jeffmhopkins/esp32-s3-touch-amoled-1.8-case/reference/waveshare-dimensions.webp

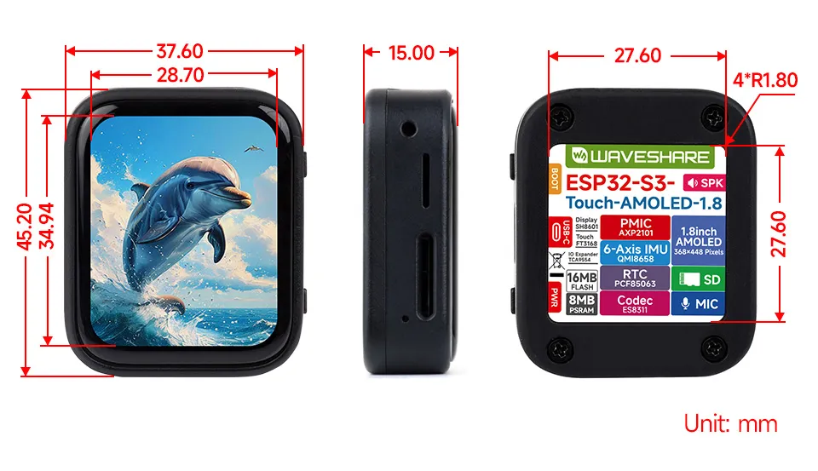
reference/waveshare-dimensions.webp
