jeffmhopkins/esp32-s3-touch-amoled-1.8-case/renders/photoreal/screens/screen_landscape.png

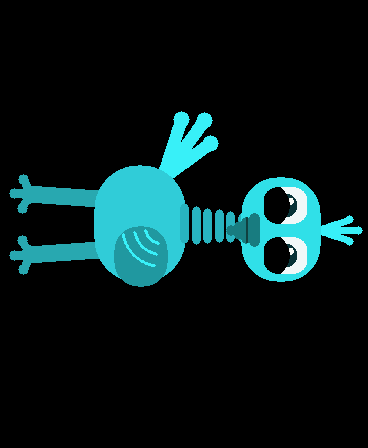
renders/photoreal/screens/screen_landscape.png
