jeffmhopkins/esp32-s3-touch-amoled-1.8-case/renders/src/fig_stand_joint.scad

// Where the head sits in the box: a side wall cut through a lock screw, drawn
// square to the head (the whole stand tilted back level).
include <../../amoled18_back_plate.scad>
use <annot.scad>
show_part = false;
$fn = 64; $k = 0.22;
lx = lock_xs[len(lock_xs) - 1];   // cut through this lock screw
v = "right"; x = lx + 2.6; t = 0.45;
m_inv = [[sc, 0, ss, -ss * stand_zh], [0, 1, 0, 0], [-ss, 0, sc, -sc * stand_zh], [0, 0, 0, 1]];
module slice() intersection() { children(); translate([lx - 0.2, 15, -6]) cube([0.4, 10, 13]); }
color("SteelBlue") render() slice() multmatrix(m_inv) stand_box();
color("LightSteelBlue") render() slice() back_plate();
// Front shell (estimated), sitting on the band round the box's angled end.
color("LightGray") translate([lx - 0.1, plate_y / 2 - 1.3, body_h]) cube([0.3, 1.3, 3.5]);
if (collar_h > 0)
    label([x, 23.9, pocket_h + 2.2], str("collar ", collar_h, " (part of the head)"), v, t, "left", c = "DimGray");
label([x, 23.9, body_h + 2.3], "front shell (ghost)", v, t, "left", c = "DimGray");
// A countersunk screw, its head flush with the band's outer face; drawn just
// in front of the cut so it shows.
color("Goldenrod") translate([lx + 0.25, plate_y / 2, lock_z]) rotate([90, 0, 0]) {
    cylinder(d = 2, h = 8);
    cylinder(d1 = 3.8, d2 = 2, h = 0.9);
}
callout([x, plate_y / 2 - 1.5, lock_z], [x, 23.9, -2.6], "M2 × 8 countersunk, flush", v, t, "left");
callout([x, 21.0, 2.8], [x, 16.0, 7.6], "pad (box) in a notch (head), 45° roof", v, t, "left");

hy = head_y / 2;
dim([x, hy + pocket_clear, pocket_h + (collar_h > 0 ? -0.5 : 0.5)], [x, plate_y / 2, pocket_h + (collar_h > 0 ? -0.5 : 0.5)], "", view = v);
if (collar_h > 0) label([x, 23.9, pocket_h + 0.8], str("pocket_wall ", pocket_wall, " (the box's band)"), v, t, "left");
else label([x, 22.1, body_h + 1.2], str("pocket_wall ", pocket_wall), v, t);
callout([x, hy + pocket_clear / 2, 2.6], [x, 23.9, 3.3], str("pocket_clear ", pocket_clear, " each side"), v, t, "left");
dim([x, bhy, -0.35], [x, hy, -0.35], "", view = v);
label([x, 19.6, -1.0], str("stand_ledge ", stand_ledge), v, t, "right");
callout([x, 18.0, 2.6], [x, 17.2, 5.2], "lock block", v, t, "right");
label([x, 17.6, -3.5], "battery room", v, t, c = "DimGray");
callout([x, hy - 0.4, 0.3], [x, 23.9, 0.6], "head's back on the ledge", v, t, "left");
